sam-rba/can-gauge-interface/fw/dac.h

/* Microchip MCP4912 10-bit DAC
 *
 * Device: PIC16F1459
 * Compiler: XC8 v3.00
 *
 * Usage:
 *
 * #include <xc.h>
 * #include <stdint.h>
 * #include "types.h"
 * #include "dac.h"
 */

// Pin mapping
#define DAC1_CS_TRIS TRISB7
#define DAC1_CS RB7
#define DAC2_CS_TRIS TRISB5
#define DAC2_CS RB5

void dacInit(void);

// Set DAC1 VOUTA.
// Mv is the desired voltage in millivolts.
void dacSet1a(U16 mv);

// Set DAC1 VOUTB.
// Mv is the desired voltage in millivolts.
void dacSet1b(U16 mv);

// Set DAC2 VOUTA.
// Mv is the desired voltage in millivolts.
void dacSet2a(U16 mv);

// Set DAC2 VOUTB.
// Mv is the desired voltage in millivolts.
void dacSet2b(U16 mv);
