sam-rba/can-gauge-interface/fw/types.h

/* Device: PIC16F1459
 * Compiler: XC8 v3.00
 *
 * Usage:
 *
 * #include <stdint.h>
 * #include "types.h"
 */

typedef enum {
	OK,
	FAIL,
} Status;

typedef uint8_t U8;
typedef uint16_t U16;
typedef uint32_t U32;
typedef int8_t I8;
typedef int16_t I16;
typedef int32_t I32;
